an-ven/K616-USB-Interface/hardware/Images/IMG_20220907_223455.jpg

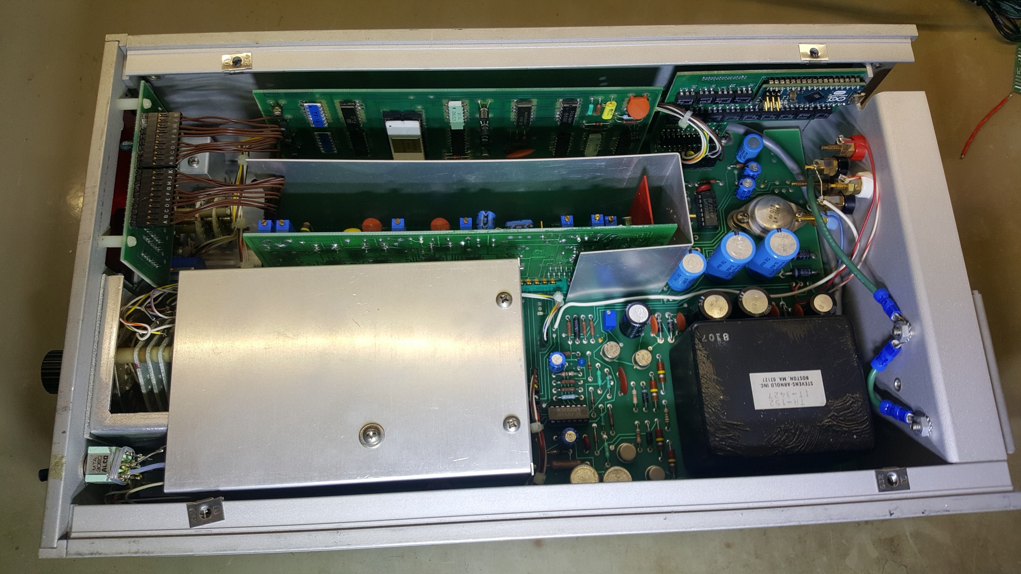
hardware/Images/IMG_20220907_223455.jpg
