an-ven/K616-USB-Interface/hardware/Images/IMG_20220907_223940.jpg

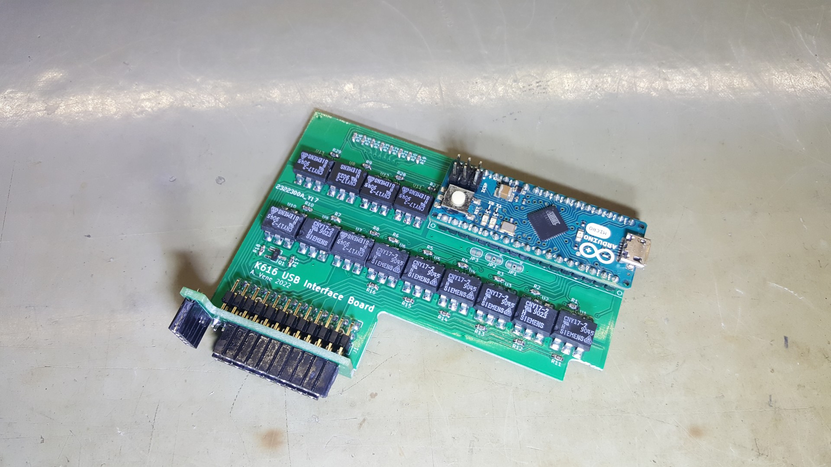
hardware/Images/IMG_20220907_223940.jpg
